gadgetstogrow/Pet_Necklace_ATTiny85/Task.cpp

/*
 * Copyright 2011 Alan Burlison, alan@bleaklow.com.  All rights reserved.
 * Use is subject to license terms.
 */

#include "Task.h"

// Virtual.
bool TriggeredTask::canRun(uint32_t now) {
    return runFlag;
}

// Virtual.
bool TimedTask::canRun(uint32_t now) {
    return now >= runTime;
}
